otitbridge/gba-dumper-esp32-s3/output/pcb/ad6_comparison/after_weact.png

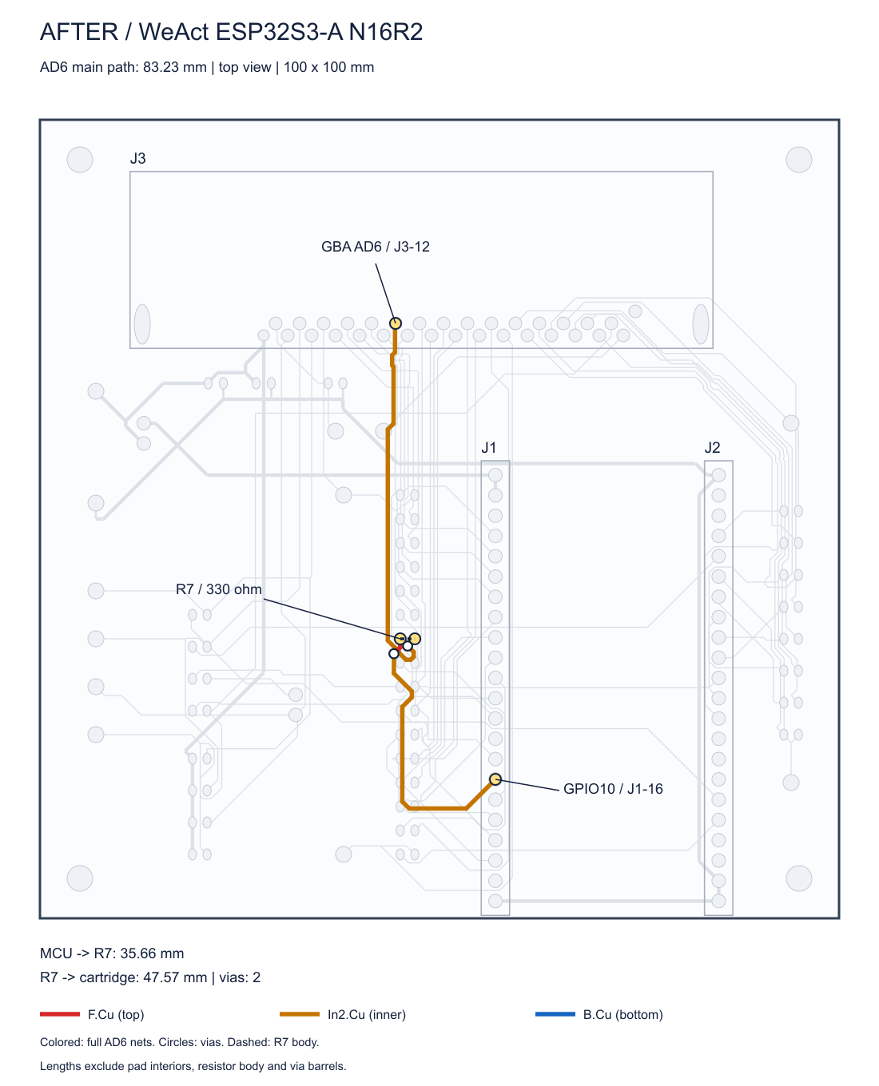
output/pcb/ad6_comparison/after_weact.png
