otitbridge/gba-dumper-esp32-s3/output/pcb/ad6_comparison/before_fnk0099.png

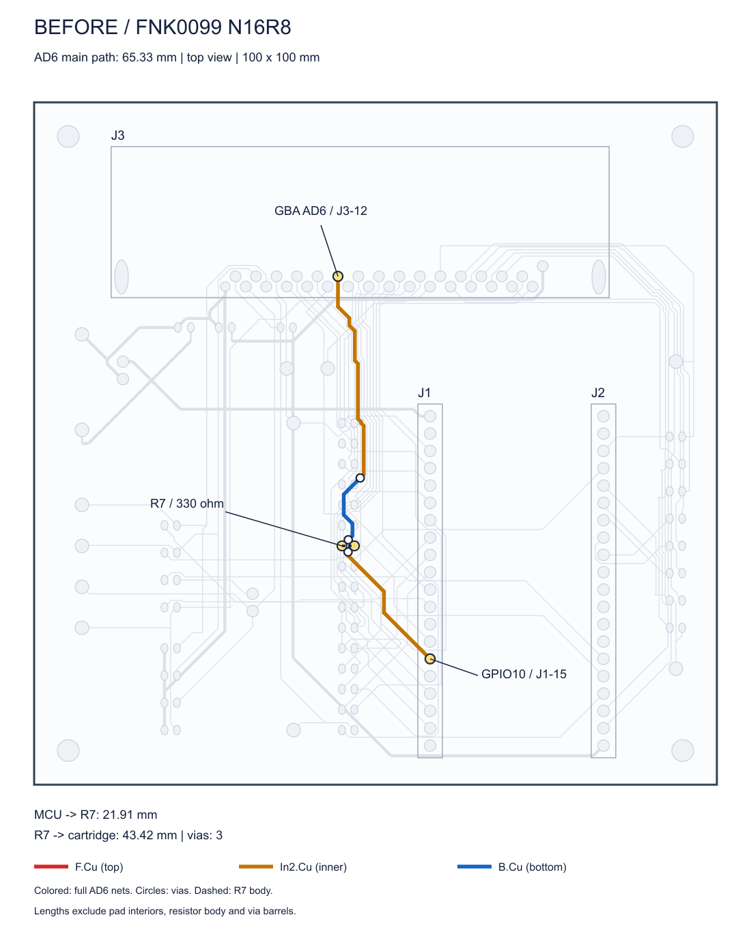
output/pcb/ad6_comparison/before_fnk0099.png
