otitbridge/gba-dumper-esp32-s3/output/pcb/ad6_comparison/comparison.png

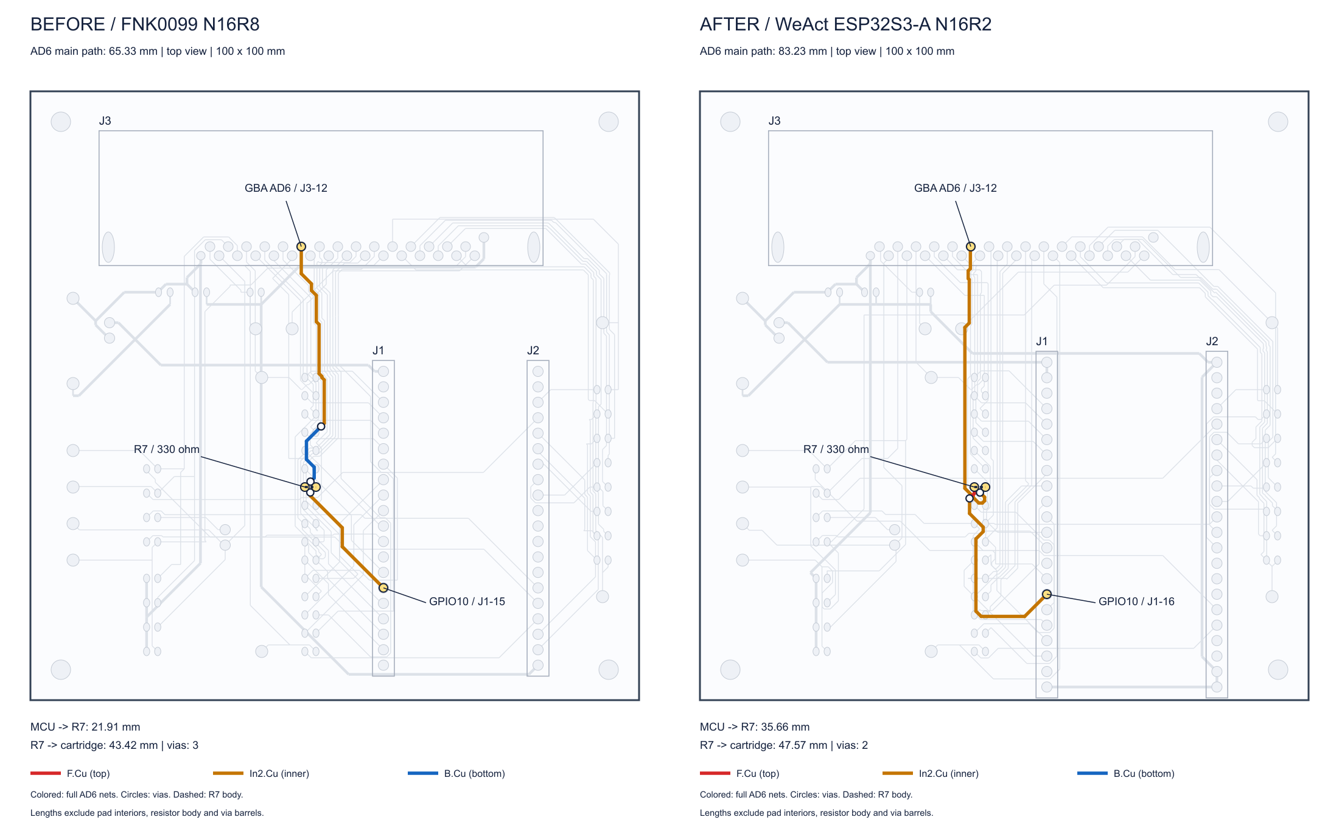
output/pcb/ad6_comparison/comparison.png
