otitbridge/gba-dumper-esp32-s3/output/pcb/ad6_rerouted_layers/four_layers.png

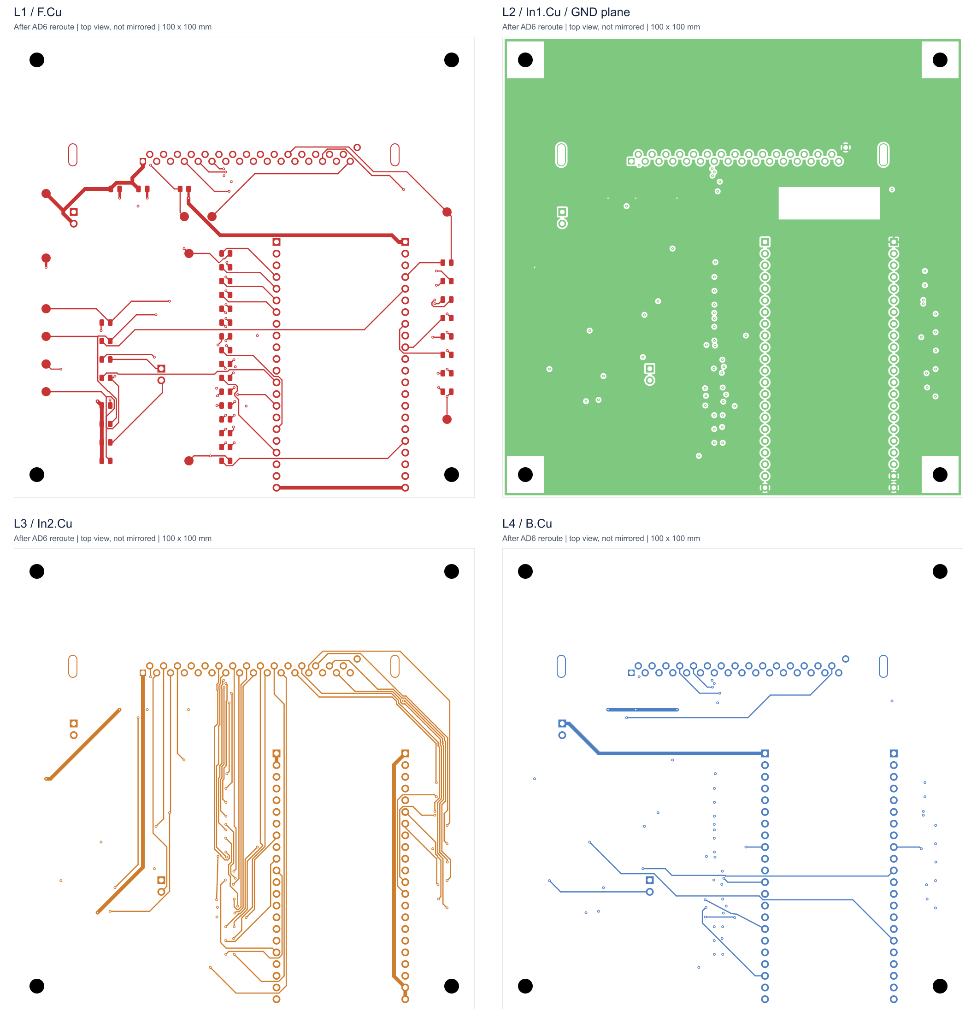
output/pcb/ad6_rerouted_layers/four_layers.png
