otitbridge/gba-dumper-esp32-s3/output/pcb/final_review/front_silk.png

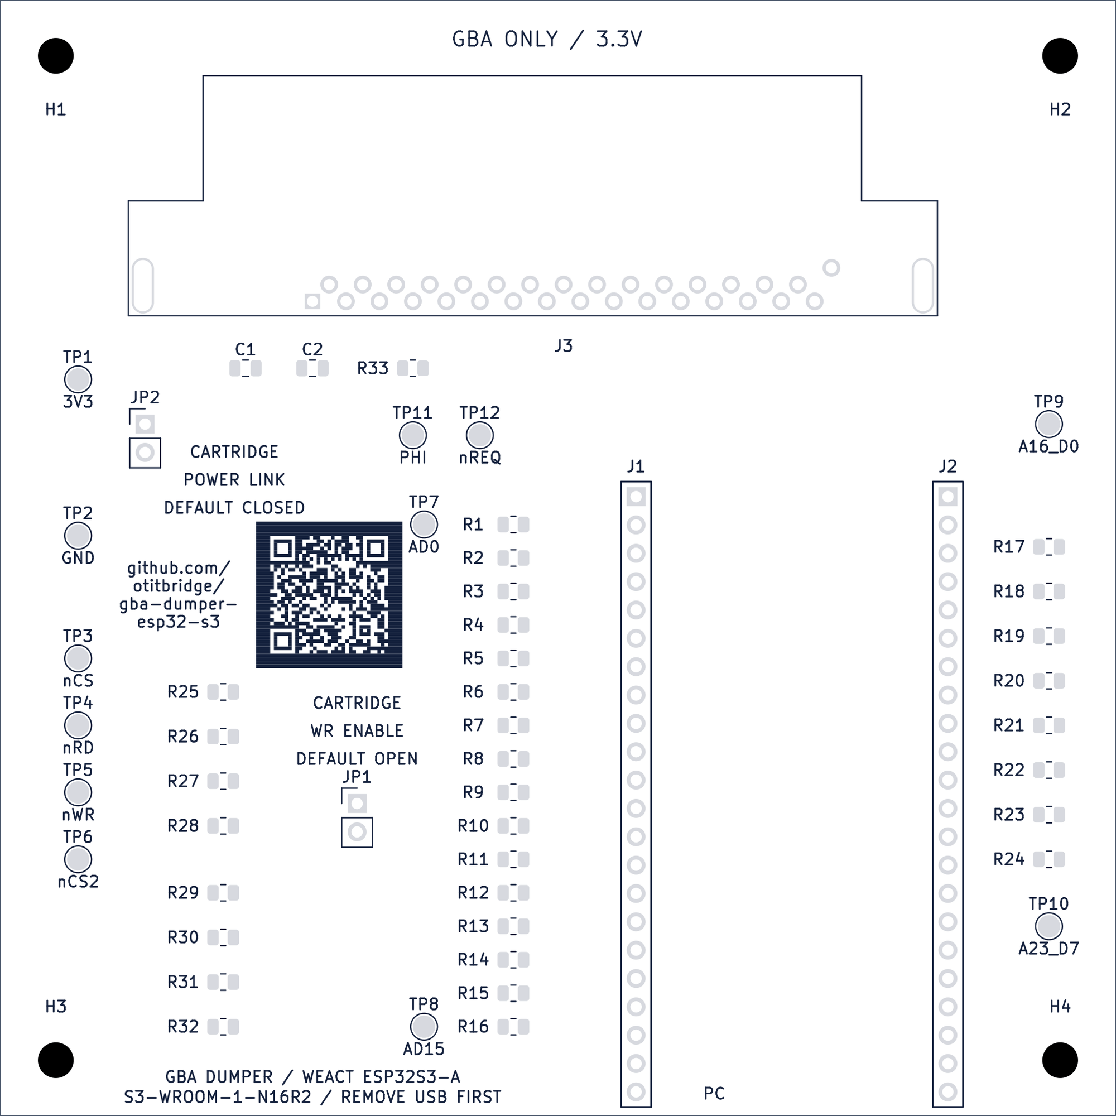
output/pcb/final_review/front_silk.png
