otitbridge/gba-dumper-esp32-s3/output/pcb/final_review/qr_decode_preview.png

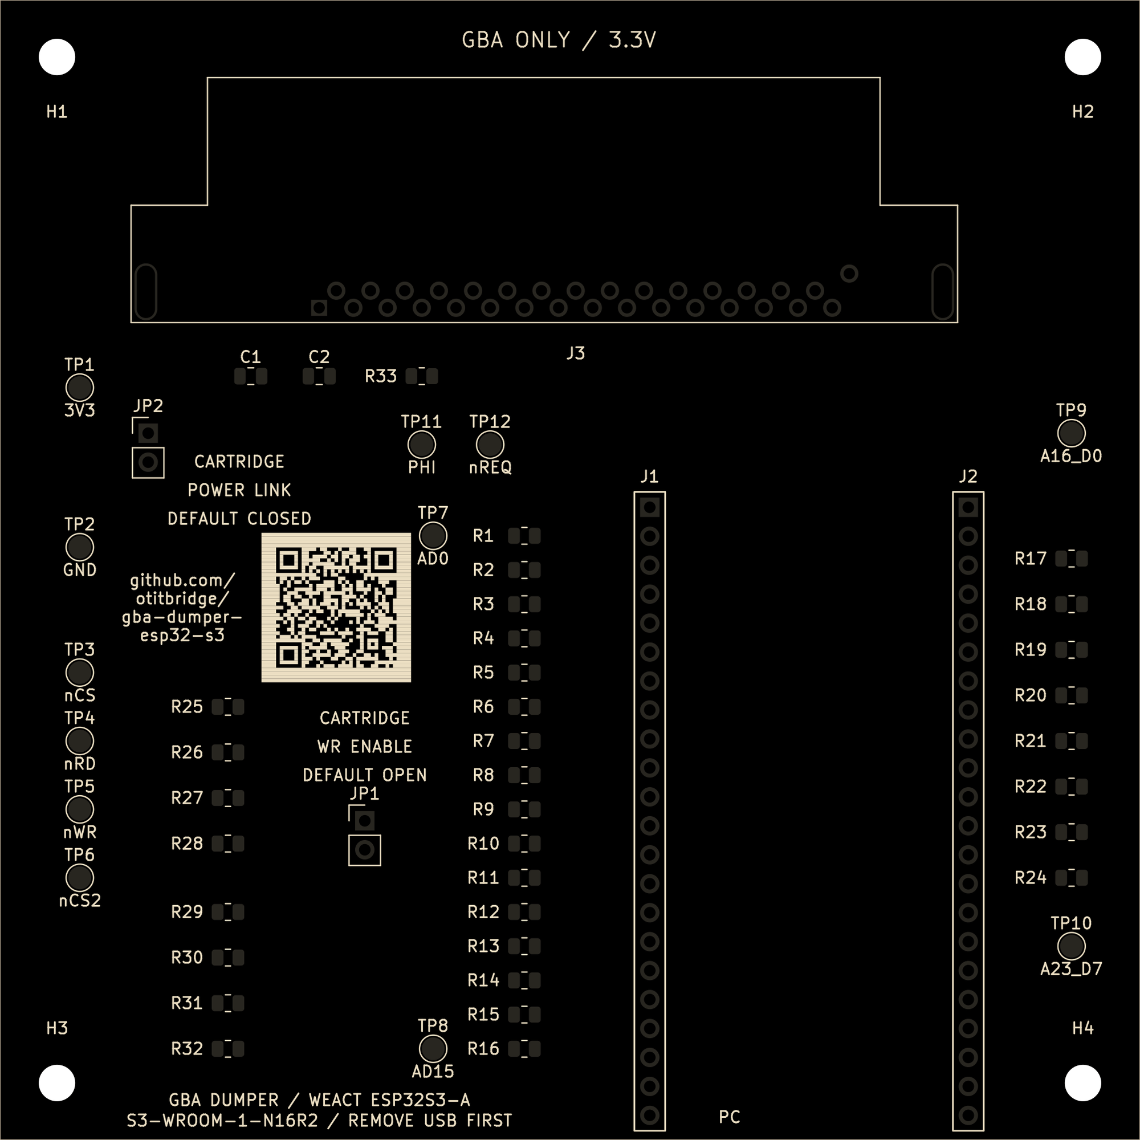
output/pcb/final_review/qr_decode_preview.png
