otitbridge/gba-dumper-esp32-s3/output/pcb/placement.png

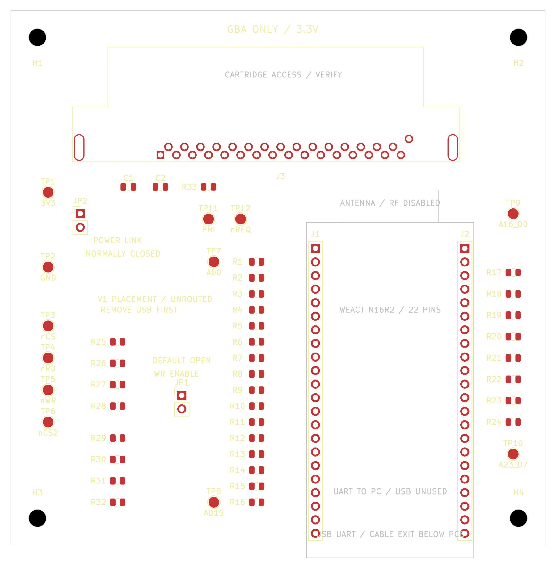
output/pcb/placement.png
