otitbridge/gba-dumper-esp32-s3/output/pcb/routed/ground_plane.png

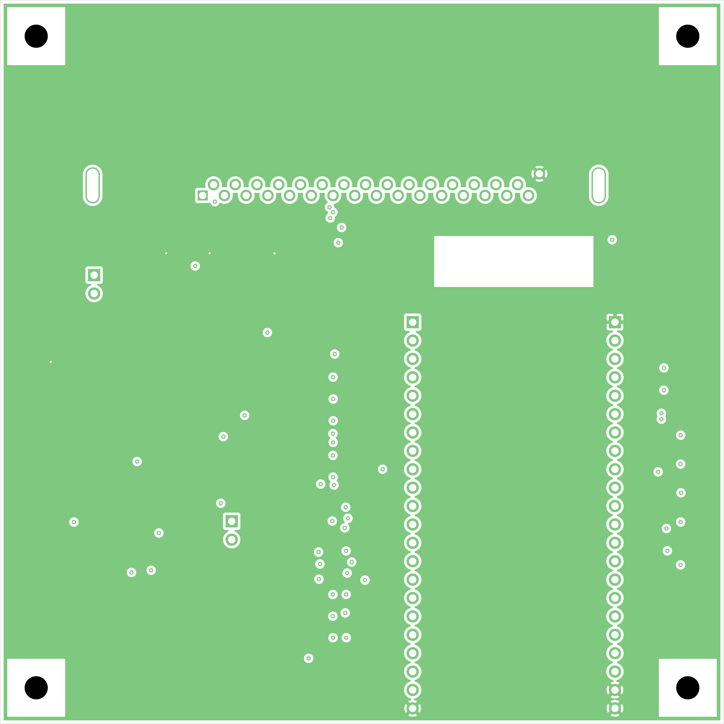
output/pcb/routed/ground_plane.png
