otitbridge/gba-dumper-esp32-s3/output/pcb/routed/routing_overview.png

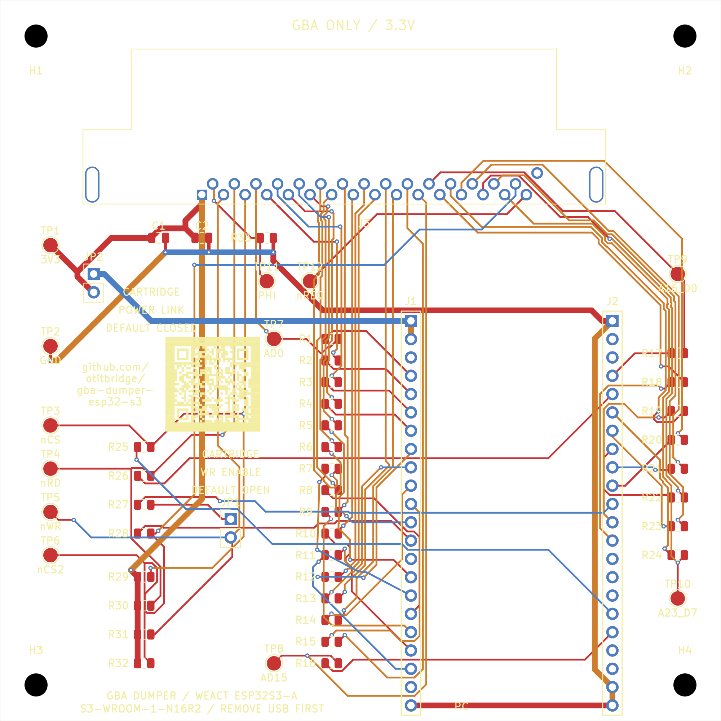
output/pcb/routed/routing_overview.png
