otitbridge/gba-dumper-esp32-s3/output/schematic/gba_dumper.png

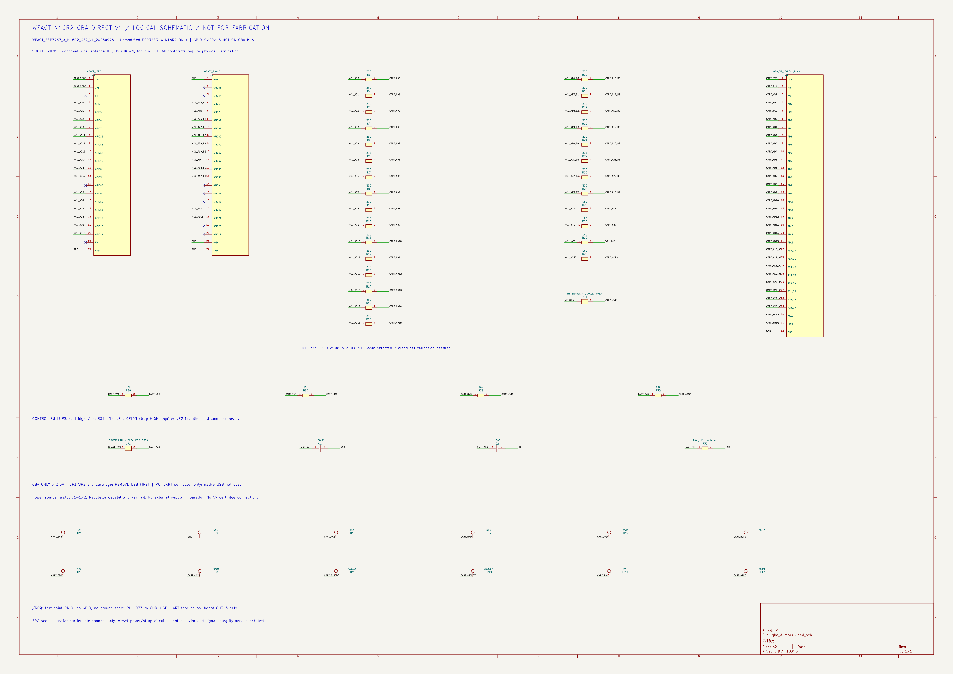
output/schematic/gba_dumper.png
