otitbridge/gba-dumper-esp32-s3/output/fabrication_review/review/gerber_silk_qr.png

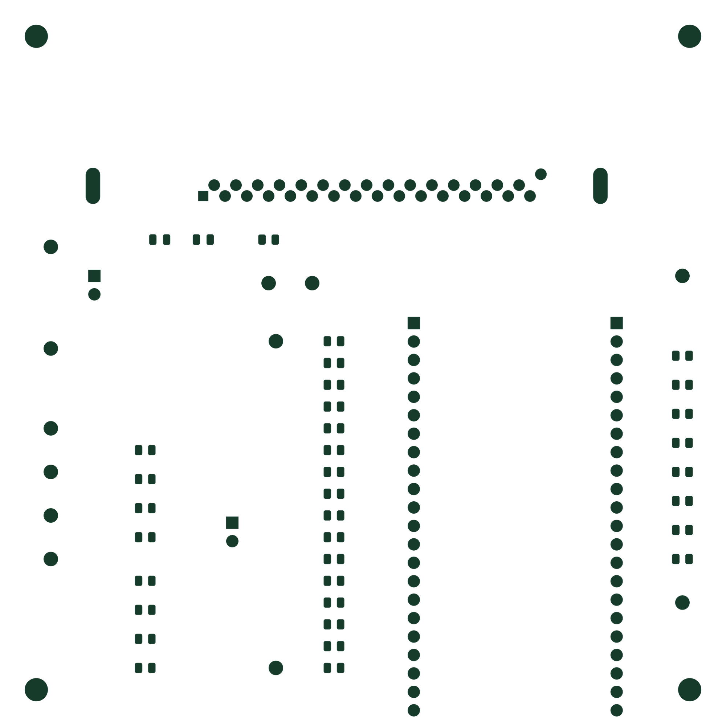
output/fabrication_review/review/gerber_silk_qr.png
