otitbridge/gba-dumper-esp32-s3/output/fabrication_review/review/gerber_top.png

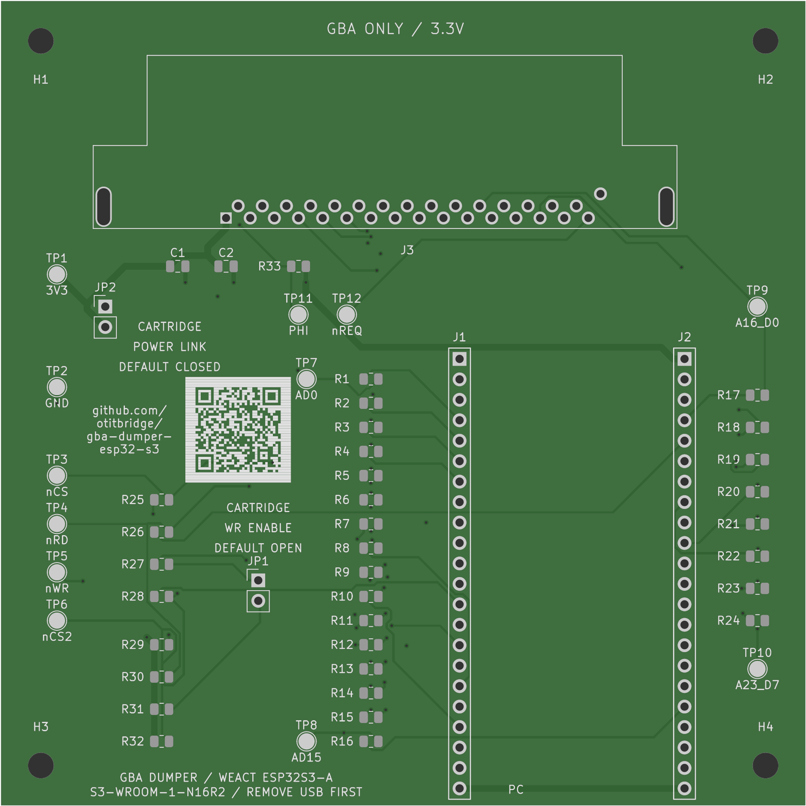
output/fabrication_review/review/gerber_top.png
